Gray-Stone/Simple-Audio-Mixer/mediaForDocs/StudyNotesMid/media/image1.png

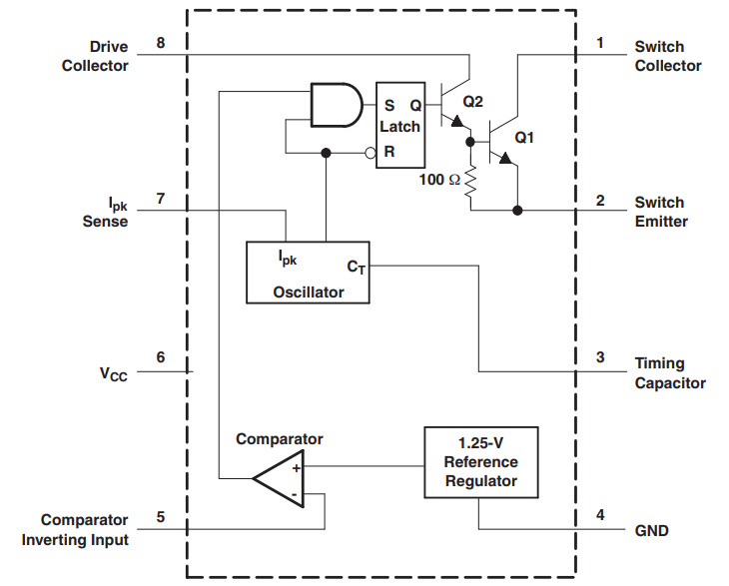
mediaForDocs/StudyNotesMid/media/image1.png
