Gray-Stone/Simple-Audio-Mixer/mediaForDocs/StudyNotesMid/media/image2.png

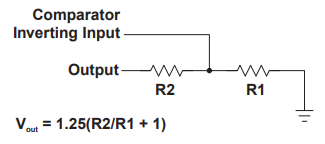
mediaForDocs/StudyNotesMid/media/image2.png
